cristoferz/ezhome/hardware/boxes/raspberry/Raspberry_Pi_B+_Sleeve_v1-1_SOLID.STL

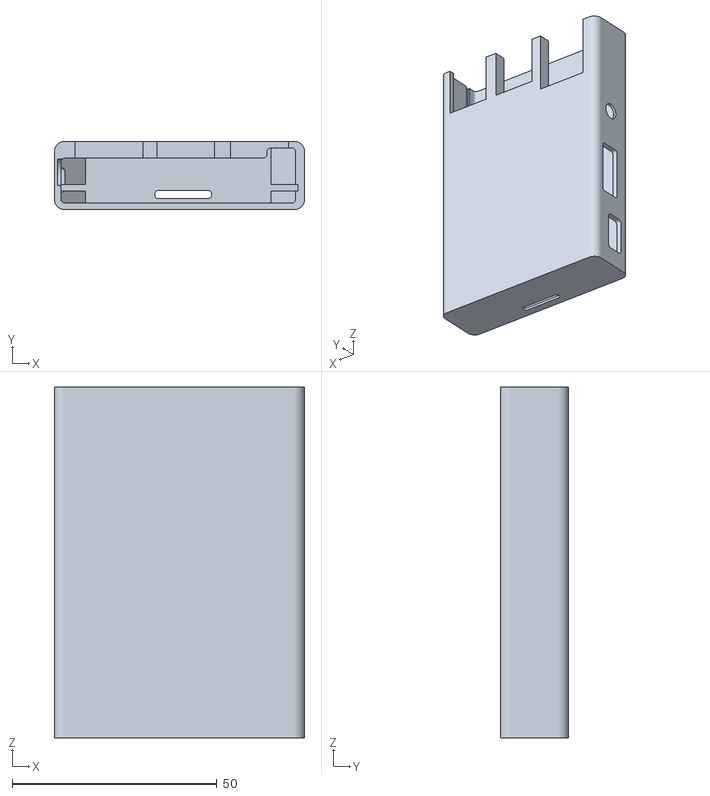
[picture p15: CAD file, 2016-06-11]
hardware/boxes/raspberry/Raspberry_Pi_B+_Sleeve_v1-1_SOLID.STL
61.2 x 16.7 x 85.8
