cristoferz/ezhome/hardware/boxes/Relays/SupportTest2.stl

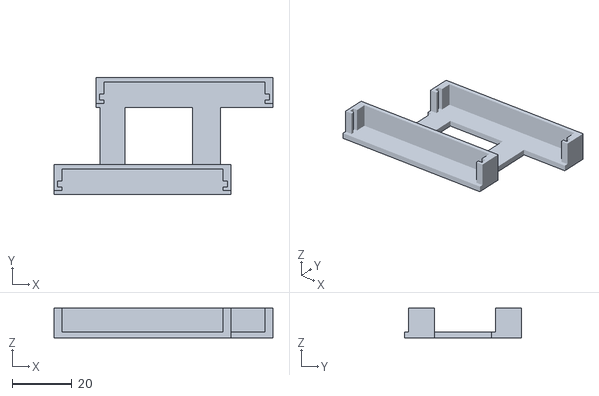
[picture p16: CAD file, 2016-06-11]
hardware/boxes/Relays/SupportTest2.stl
73.0 x 39.0 x 10.0
