cristoferz/ezhome/hardware/maquete/Roof_002.STL

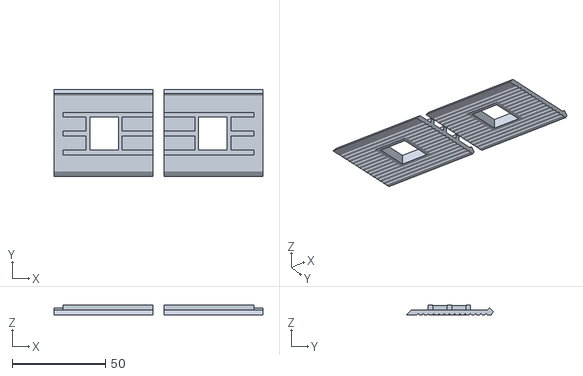
[picture p17: CAD file, 2016-06-11]
hardware/maquete/Roof_002.STL
112.1 x 46.5 x 5.11
