cristoferz/ezhome/hardware/boxes/Parts/Base.fcstd

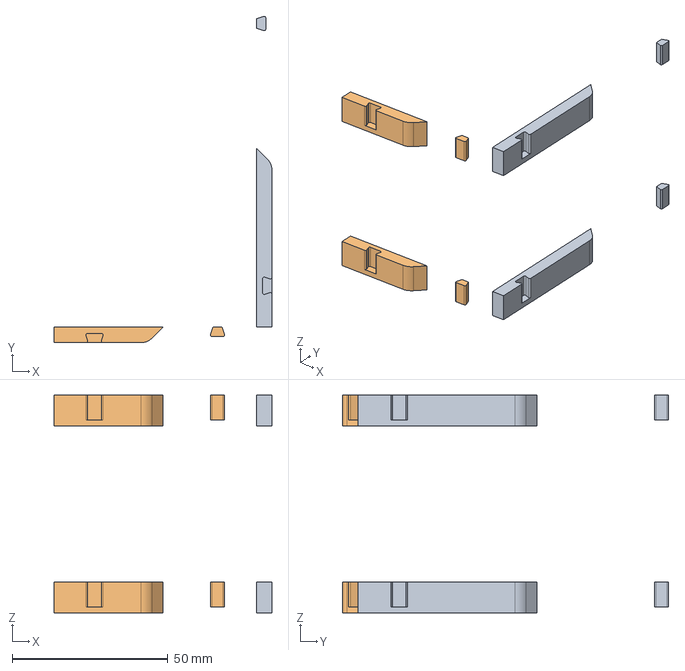
[picture p18: CAD file, 2016-06-11]
hardware/boxes/Parts/Base.fcstd
70.0 x 104.8 x 70.0 mm
Conectores Maiores
Conectores Menores
