cristoferz/ezhome/hardware/boxes/raspberry/rpi2-bottom_8020_netfabb.stl

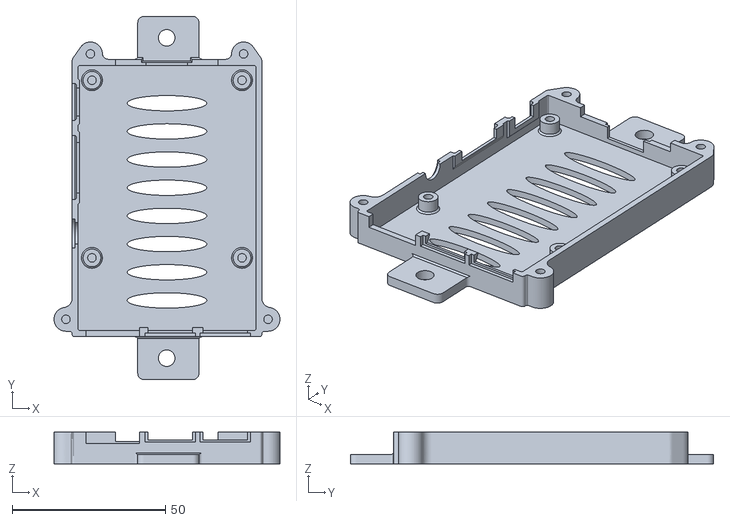
[picture p19: CAD file, 2016-06-11]
hardware/boxes/raspberry/rpi2-bottom_8020_netfabb.stl
73.8 x 118.6 x 10.3
