cristoferz/ezhome/hardware/maquete/Walls_002.STL

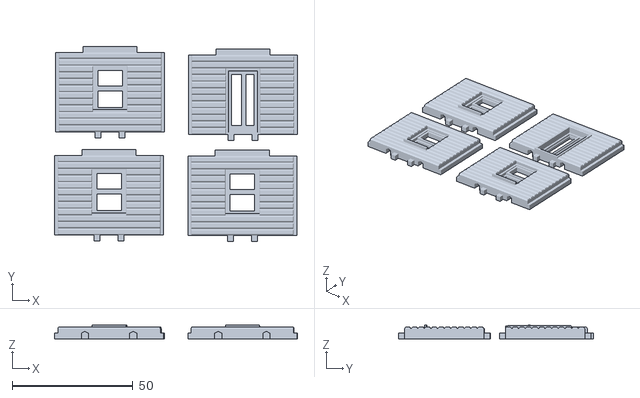
[picture p20: CAD file, 2016-06-11]
hardware/maquete/Walls_002.STL
100.8 x 80.9 x 6.00
