cristoferz/ezhome/hardware/boxes/raspberry/rpi2-bottom_100mm-vesa_netfabb.stl

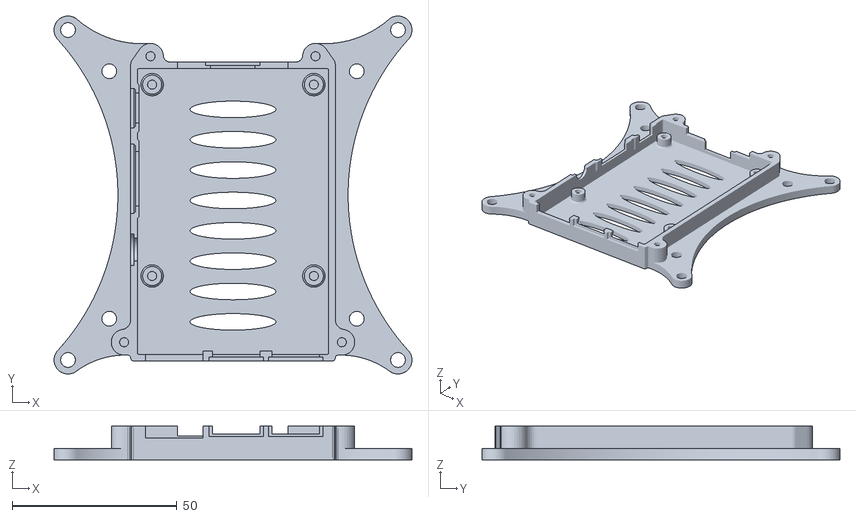
[picture p21: CAD file, 2016-06-11]
hardware/boxes/raspberry/rpi2-bottom_100mm-vesa_netfabb.stl
108.5 x 108.5 x 10.3
