cristoferz/ezhome/hardware/boxes/Relays/4-Relay-Cover.stl

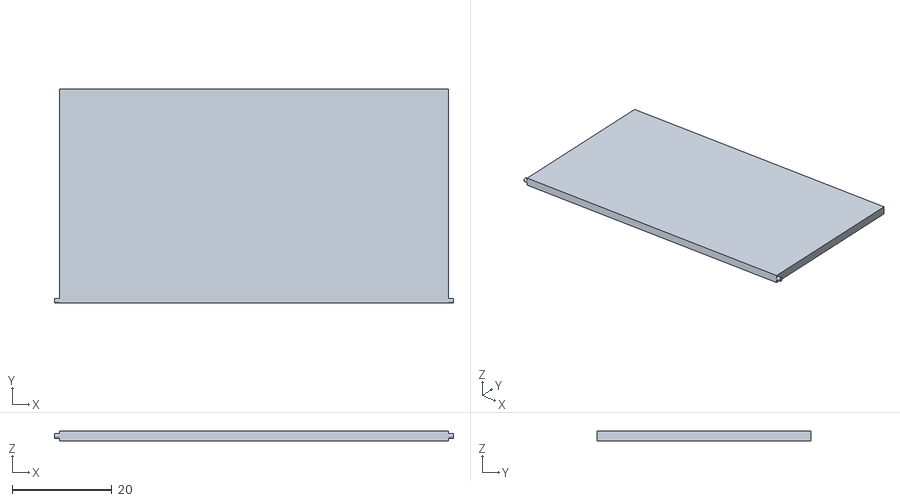
[picture p22: CAD file, 2016-06-11]
hardware/boxes/Relays/4-Relay-Cover.stl
80.0 x 43.0 x 2.00
