cristoferz/ezhome/hardware/maquete/Slabs_001.STL

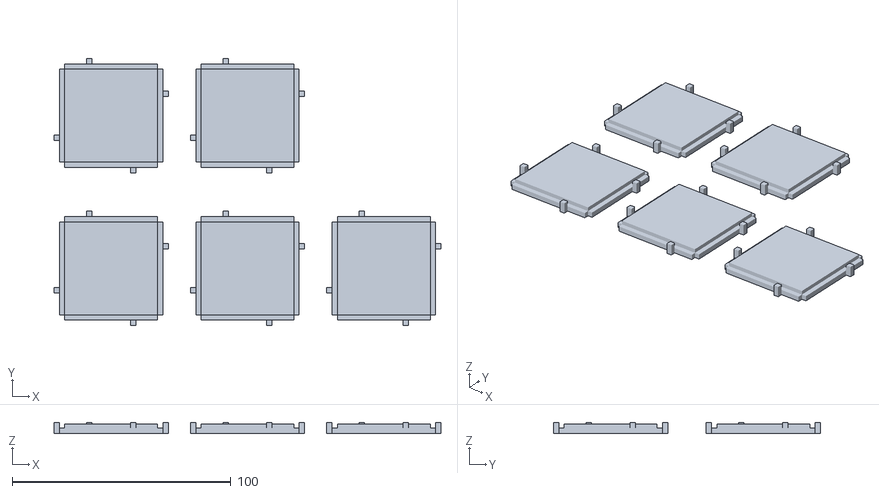
[picture p23: CAD file, 2016-06-11]
hardware/maquete/Slabs_001.STL
176.8 x 121.9 x 5.20
