cristoferz/ezhome/hardware/boxes/raspberry/rpi2-top_30mm-fan_netfabb.stl

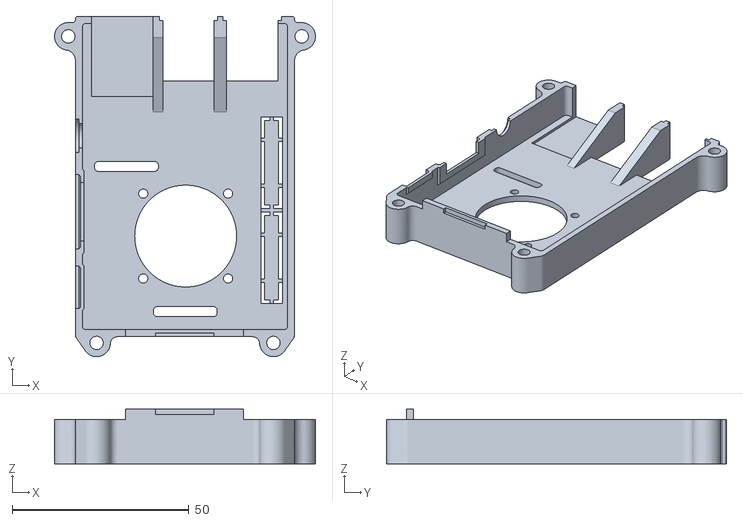
[picture p24: CAD file, 2016-06-11]
hardware/boxes/raspberry/rpi2-top_30mm-fan_netfabb.stl
73.8 x 96.2 x 15.5
