cristoferz/ezhome/hardware/boxes/Relays/SupportTest.fcstd

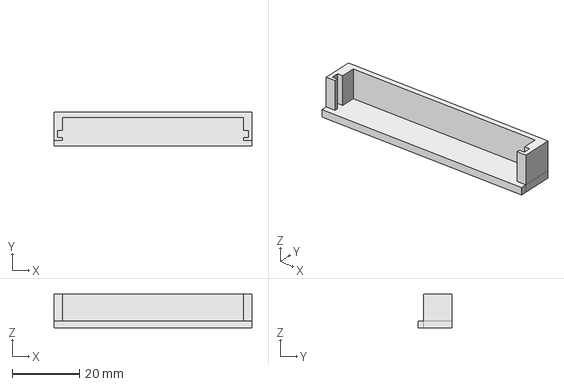
[picture p25: CAD file, 2016-06-11]
hardware/boxes/Relays/SupportTest.fcstd
59.0 x 10.0 x 10.0 mm
