cristoferz/ezhome/hardware/maquete/Roof_001.STL

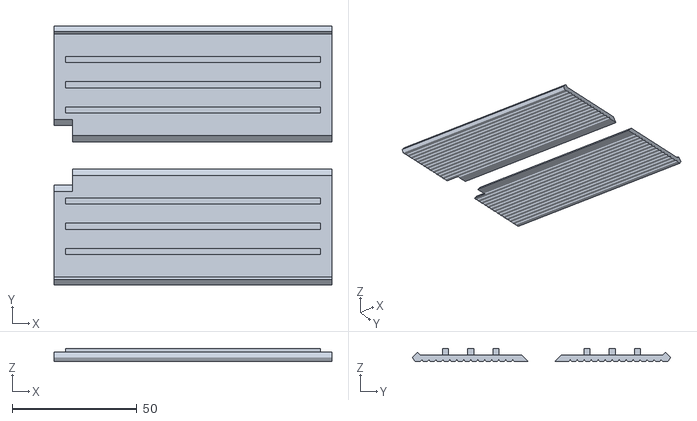
[picture p26: CAD file, 2016-06-11]
hardware/maquete/Roof_001.STL
111.6 x 103.9 x 5.11
