cristoferz/ezhome/hardware/maquete/Beams_001.STL

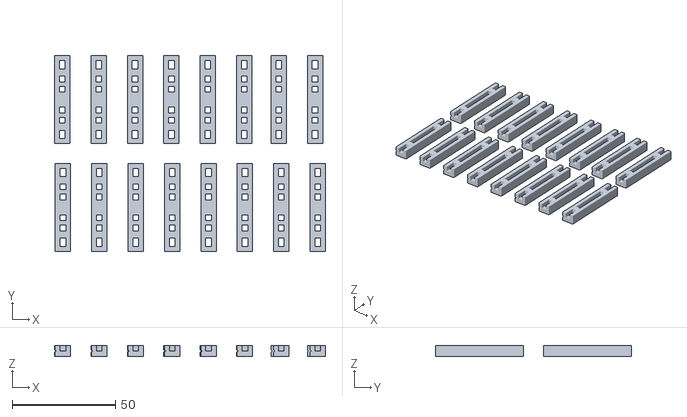
[picture p28: CAD file, 2016-06-11]
hardware/maquete/Beams_001.STL
131.1 x 94.6 x 5.50
