cristoferz/ezhome/hardware/maquete/Walls_001.STL

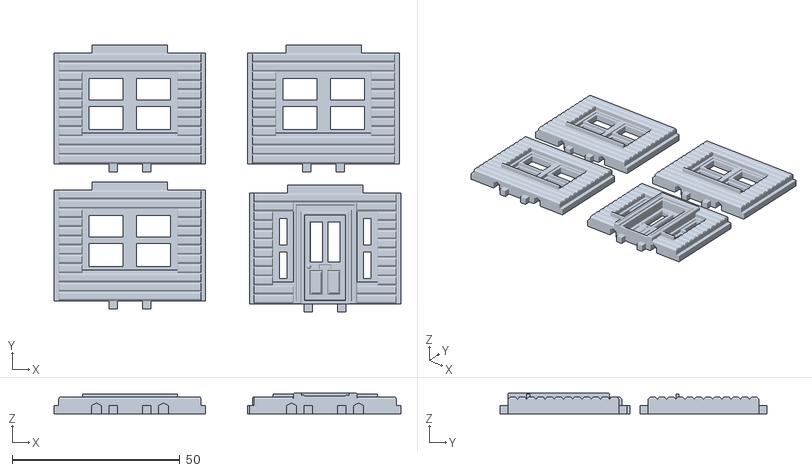
[picture p30: CAD file, 2016-06-11]
hardware/maquete/Walls_001.STL
103.5 x 79.7 x 6.23
