cristoferz/ezhome/hardware/boxes/raspberry/MEGA_R2_MOUNT.STL

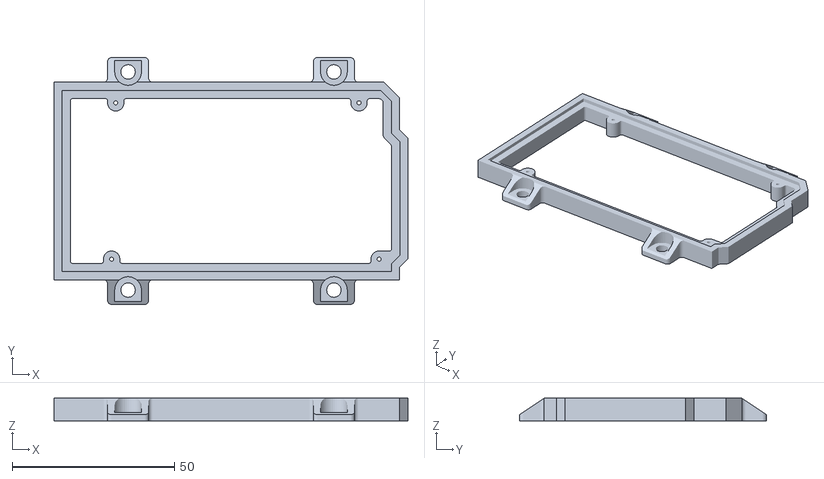
[picture p31: CAD file, 2016-06-11]
hardware/boxes/raspberry/MEGA_R2_MOUNT.STL
109.2 x 76.2 x 6.99
