cristoferz/ezhome/hardware/maquete/Walls_003.STL

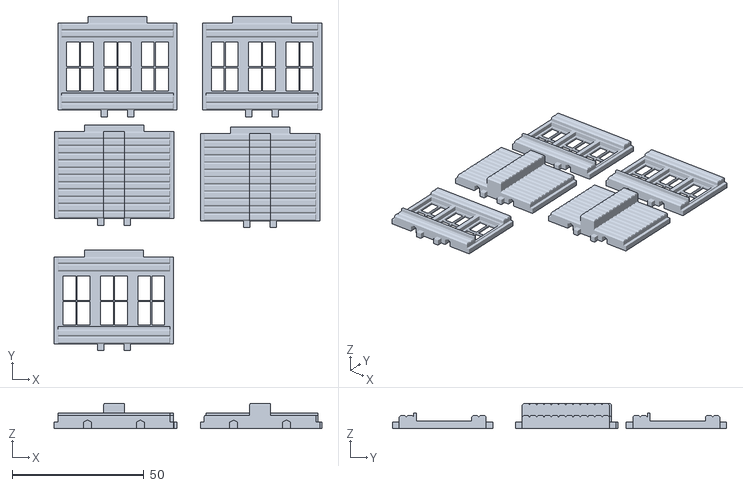
[picture p32: CAD file, 2016-06-11]
hardware/maquete/Walls_003.STL
101.4 x 126.6 x 9.60
