cristoferz/ezhome/hardware/maquete/Roof_walls_001.STL

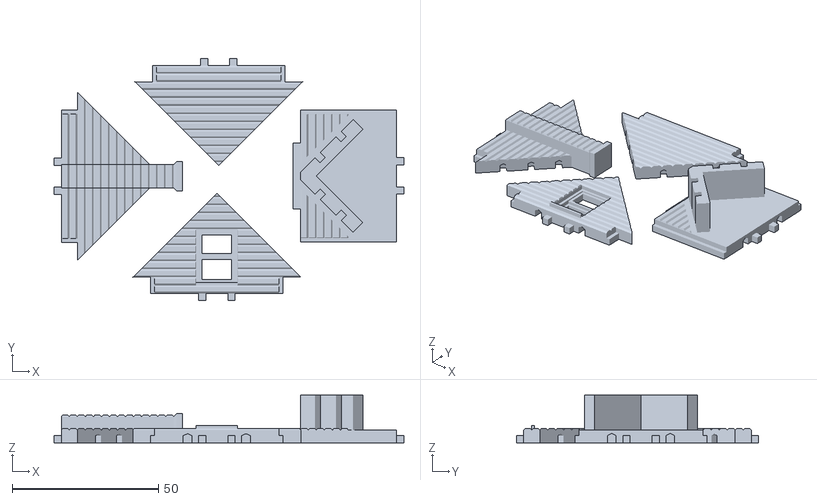
[picture p33: CAD file, 2016-06-11]
hardware/maquete/Roof_walls_001.STL
119.8 x 82.9 x 16.4
